Haptic-Solutions/BTMSrev1_4s/REV1AP/EVBatteryCTRLv01D.X/errorCodes.h

/*Copyright (c) <2024> <Jarrett Cigainero>

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
THE SOFTWARE IS PROVIDED "AS IS", WITHOUT WARRANTY OF ANY KIND, EXPRESS OR
IMPLIED, INCLUDING BUT NOT LIMITED TO THE WARRANTIES OF MERCHANTABILITY,
FITNESS FOR A PARTICULAR PURPOSE AND NONINFRINGEMENT. IN NO EVENT SHALL THE
AUTHORS OR COPYRIGHT HOLDERS BE LIABLE FOR ANY CLAIM, DAMAGES OR OTHER
LIABILITY, WHETHER IN AN ACTION OF CONTRACT, TORT OR OTHERWISE, ARISING FROM,
OUT OF OR IN CONNECTION WITH THE SOFTWARE OR THE USE OR OTHER DEALINGS IN THE
SOFTWARE. */

#ifndef ERRORCODES_H
#define	ERRORCODES_H

const char code01[] = "Heater too small for the watts you want.";
const char code02[] = "No heater detected.";
const char code03[] = "Heater too large or short circuit detected.";
const char code04[] = "Low Batt Voltage";
const char code05[] = "Batt Over Current";
const char code06[] = "Batt Charge Over Current";
const char code07[] = "Software Batt HV Detect";
const char code08[] = "Batt Over Temp";
const char code09[] = "B-Flag(s) Set: System locked out.";
const char code0A[] = "Self Over Temp";
const char code0B[] = "Sys Shutdown";
const char code0C[] = "PWM excep";
const char code0D[] = "Osc excep";
const char code0E[] = "Addr excep";
const char code0F[] = "STK excep";
const char code10[] = "MTH excep";
const char code11[] = "Res7 excep";
const char code12[] = "Disp Buffer Err";
const char code13[] = "MCU BrownOut";
const char code14[] = "WDT rst";
const char code15[] = "un-handled exception rst";
const char code16[] = "Opcode rst";
const char code17[] = "MCLR rst";
const char code18[] = "Illegal Inst";
const char code19[] = "Sys Rst";
const char code1A[] = "Inval serial port";
const char code1B[] = "USB Chrg Fault";
const char code1C[] = "PChg set > 100%: Clamping.";
const char code1D[] = "VH ChrgVlt";
const char code1E[] = "VL ChrgVlt";
const char code1F[] = "VH ChrgCrnt";
const char code20[] = "VL ChrgCrnt";
const char code21[] = "VH BtryTmp";
const char code22[] = "VL BtryTmp";
const char code23[] = "VH BtryCrnt";
const char code24[] = "VL BtryCrnt";
const char code25[] = "VH SysTmp";
const char code26[] = "VL SysTmp";
const char code27[] = "PORT1 BSY err";
const char code28[] = "PORT2 BSY err";
const char code29[] = "Pgm Chksum Err";
const char code2A[] = "NVM Chksum Err";
const char code2B[] = "Sets Chksum Err";
const char code2C[] = "NVS Chksum Err";
const char code2D[] = "PORT1 ERR";
const char code2E[] = "PORT2 ERR";
const char code2F[] = "Soft Over Current";
const char code30[] = "VH S1Vlt";
const char code31[] = "VL S1Vlt";
const char code32[] = "VH S2Vlt";
const char code33[] = "VL S2Vlt";
const char code34[] = "VH S3Vlt";
const char code35[] = "VL S3Vlt";
const char code36[] = "VH S4Vlt";
const char code37[] = "VL S4Vlt";
const char code38[] = "Charger input Over Volt";
const char code39[] = "Hardware OverCrnt Shutdown: Unplug source, & turn power off for 20 seconds to reset.";
const char code3A[] = "Hardware OverVolt Shutdown: Battery Safety Fuse Tripped. Unit must be serviced.";
const char code3B[] = "Battery Under Voltage Lockout";
const char code3C[] = "Charger power has cycled too many times. Aborting for now.";
const char code3D[] = "Sys Safe Mode. Minimum Debug Functionality.";
const char code3E[] = "Port Sanity Error";
const char code3F[] = "I2C Sequence Error";
const char code40[] = "I2C Timeout";
const char code41[] = "I2C bus not idle";
const char code42[] = "I2C bus collision";
const char code43[] = "I2C ACK Error";
const char code44[] = "Load shutdown before cycle complete. Aborting Evaluation.";
const char code45[] = "Parameters not right for auto evaluation. Aborting Evaluation.";
const char codeDefault[] = "Unknown";

const char * const errArray[] = {code01,code02,code03,code04,code05,code06,code07,code08,code09,code0A,code0B,code0C
                         ,code0D,code0E,code0F,code10,code11,code12,code13,code14,code15,code16,code17,code18
                         ,code19,code1A,code1B,code1C,code1D,code1E,code1F,code20,code21,code22,code23,code24
                         ,code25,code26,code27,code28,code29,code2A,code2B,code2C,code2D,code2E,code2F,code30
                         ,code31,code32,code33,code34,code35,code36,code37,code38,code39,code3A,code3B,code3C
                         ,code3D,code3E,code3F,code40,code41,code42,code43,code44,code45,codeDefault};

#endif	/* ERRORCODES_H */
